sparkfun/SparkFun_GNSS_Combo_Breakout-ZED-F9P_NEO-D9S/docs/assets/imgs/22560-GPS-SparkFun-u-blox-ZED-F9P-NEO-D9S-Combo-Breakout-02-HIGH-RES.jpg

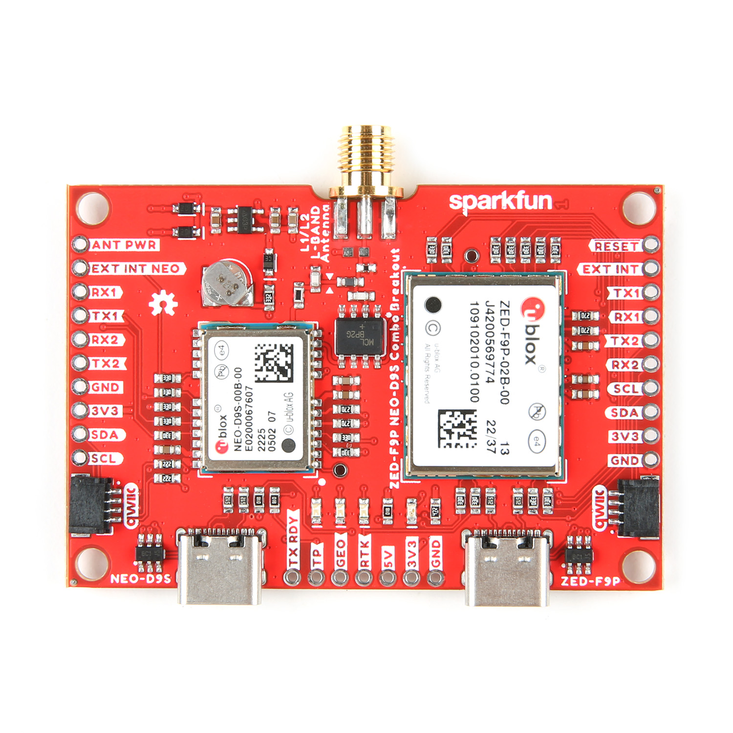
docs/assets/imgs/22560-GPS-SparkFun-u-blox-ZED-F9P-NEO-D9S-Combo-Breakout-02-HIGH-RES.jpg
