sparkfun/SparkFun_GNSS_Combo_Breakout-ZED-F9P_NEO-D9S/docs/assets/imgs/22560-SparkFun_u-blox_ZED-F9P_NEO-D9S_Combo-Bottom.jpg

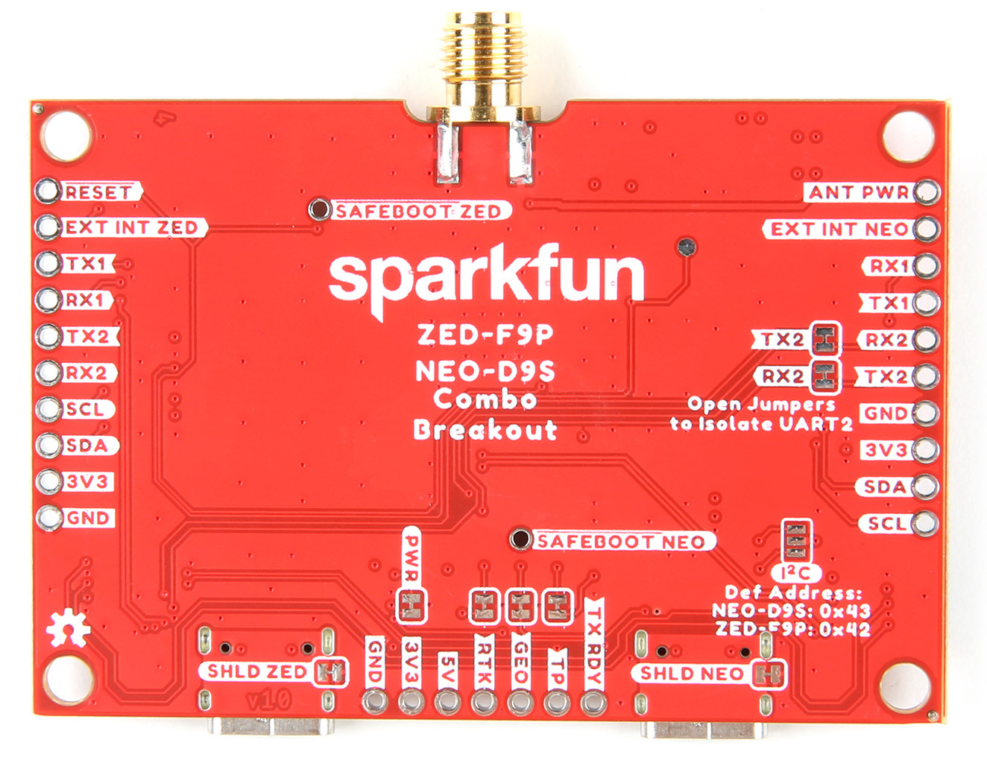
docs/assets/imgs/22560-SparkFun_u-blox_ZED-F9P_NEO-D9S_Combo-Bottom.jpg
